pablolignelli/pico-oruga-platformio-espidf/docs/oruga_board.kicad_sch

## KiCad design docs/oruga_board.kicad_sch (2026-09-04)

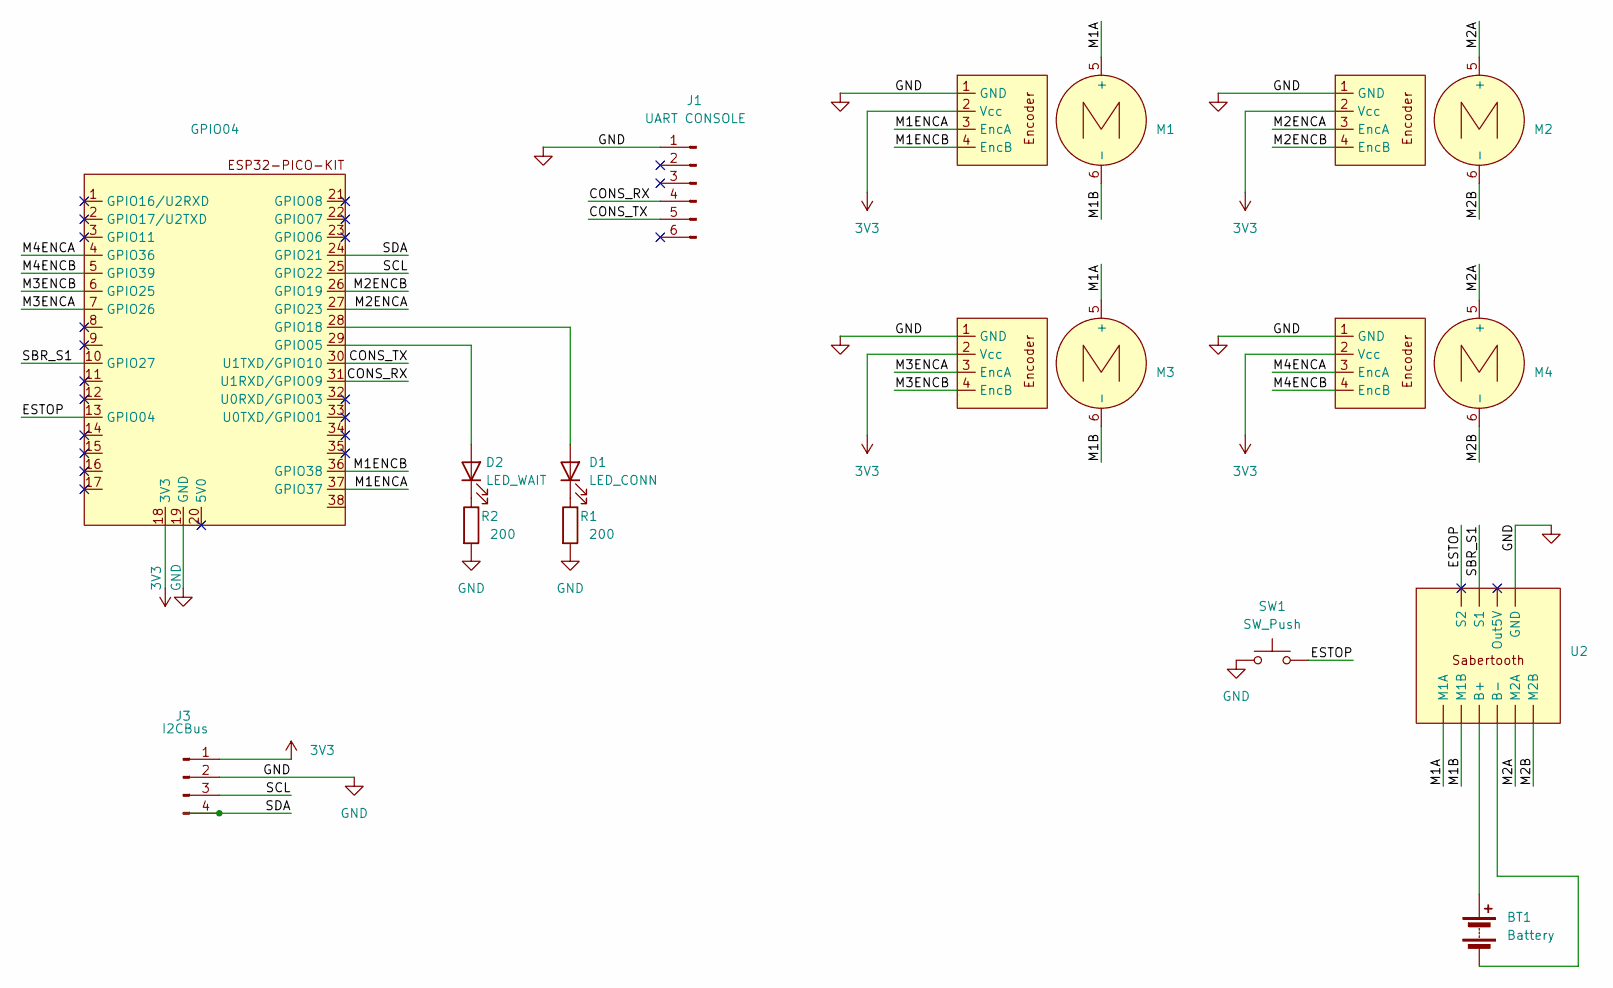
[picture p3: schematic oruga_board.kicad_sch]

Parts:
BT1: Battery
D1: LED_CONN
D2: LED_WAIT
GPIO04: (no value)
J1: UART CONSOLE
J3: I2CBus
M1: M1
M2: M2
M3: M3
M4: M4
R1, R2: 200
SW1: SW_Push
U2: (no value)

Connections:
3V3: GPIO04.18 (3V3), J3.1, M1.2 (Vcc), M2.2 (Vcc), M3.2 (Vcc), M4.2 (Vcc)
CONS_RX: GPIO04.31 (U1RXD/GPIO09), J1.4
CONS_TX: GPIO04.30 (U1TXD/GPIO10), J1.5
ESTOP: GPIO04.13 (GPIO04), SW1.2, U2.
GND: GPIO04.19 (GND), J1.1, J3.2, M1.1 (GND), M2.1 (GND), M3.1 (GND), M4.1 (GND), R1.2, R2.2, SW1.1, U2.
M1A: M1.5 (+), M3.5 (+), U2.
M1B: M1.6 (-), M3.6 (-), U2.
M1ENCA: GPIO04.37 (GPIO37), M1.3 (EncA)
M1ENCB: GPIO04.36 (GPIO38), M1.4 (EncB)
M2A: M2.5 (+), M4.5 (+), U2.
M2B: M2.6 (-), M4.6 (-), U2.
M2ENCA: GPIO04.27 (GPIO23), M2.3 (EncA)
M2ENCB: GPIO04.26 (GPIO19), M2.4 (EncB)
M3ENCA: GPIO04.7 (GPIO26), M3.3 (EncA)
M3ENCB: GPIO04.6 (GPIO25), M3.4 (EncB)
M4ENCA: GPIO04.4 (GPIO36), M4.3 (EncA)
M4ENCB: GPIO04.5 (GPIO39), M4.4 (EncB)
unnamed: BT1.1 (+), U2.
unnamed: BT1.2 (-), U2.
unnamed: D1.1 (K), R1.1
unnamed: D1.2 (A), GPIO04.28 (GPIO18)
unnamed: D2.1 (K), R2.1
unnamed: D2.2 (A), GPIO04.29 (GPIO05)
SBR_S1: GPIO04.10 (GPIO27), U2.
SCL: GPIO04.25 (GPIO22), J3.3
SDA: GPIO04.24 (GPIO21), J3.4
