pablolignelli/pico-oruga-platformio-espidf/src/wifi_connection.cpp

#include "wifi_connection.h"

#include <esp_log.h>
#include <esp_netif.h>
#include <esp_event.h>
#include <esp_wifi.h>
#include <string.h>

static const char *TAG = "wifi";
bool WifiConnection::connected = false;

static void NetworkEventHandler(void *arg, esp_event_base_t event_base,
                                int32_t event_id, void *event_data)
{
    if (event_base == WIFI_EVENT && event_id == WIFI_EVENT_STA_START)
    {
        esp_wifi_connect();
    }
    else if (event_base == WIFI_EVENT && event_id == WIFI_EVENT_STA_DISCONNECTED)
    {
        esp_wifi_connect();
        ESP_LOGD(TAG, "Retrying to connect to Wifi...");
    }
    else if (event_base == IP_EVENT && event_id == IP_EVENT_STA_GOT_IP)
    {
        ip_event_got_ip_t *event = (ip_event_got_ip_t *)event_data;
        ESP_LOGI(TAG, "got ip:" IPSTR, IP2STR(&event->ip_info.ip));
        WifiConnection::connected = true;
    }
}

WifiConnection::WifiConnection() {}

void WifiConnection::connect(const char *ssid, const char *password)
{
    // Initialize TCP/IP network interface (required for Wi-Fi)
    ESP_ERROR_CHECK(esp_netif_init());

    // Initialize the event loop
    ESP_ERROR_CHECK(esp_event_loop_create_default());
    esp_netif_create_default_wifi_sta();

    // Initialize Wi-Fi
    wifi_init_config_t cfg = WIFI_INIT_CONFIG_DEFAULT();
    ESP_ERROR_CHECK(esp_wifi_init(&cfg));

    // Set Wi-Fi to station mode
    ESP_ERROR_CHECK(esp_wifi_set_mode(WIFI_MODE_STA));

    // Configure the Wi-Fi connection
    wifi_config_t wifi_config = {};
    strncpy((char *)wifi_config.sta.ssid, ssid, 32);
    strncpy((char *)wifi_config.sta.password, password, 64);
    /*wifi_config_t wifi_config = {
        .sta = {
            .ssid = "pelleport",
            .password = "lapaz50LAPAZ50"
        }
    };*/

    // Register event handler
    ESP_ERROR_CHECK(esp_event_handler_instance_register(WIFI_EVENT,
                                                        ESP_EVENT_ANY_ID,
                                                        &NetworkEventHandler,
                                                        NULL,
                                                        NULL));
    ESP_ERROR_CHECK(esp_event_handler_instance_register(IP_EVENT,
                                                        IP_EVENT_STA_GOT_IP,
                                                        &NetworkEventHandler,
                                                        NULL,
                                                        NULL));

    // Set Wi-Fi configuration and start Wi-Fi
    ESP_ERROR_CHECK(esp_wifi_set_config(WIFI_IF_STA, &wifi_config));
    ESP_ERROR_CHECK(esp_wifi_start());
}
